StefansAI/LCD-DisplayController/docs/assets/images/photo2.png

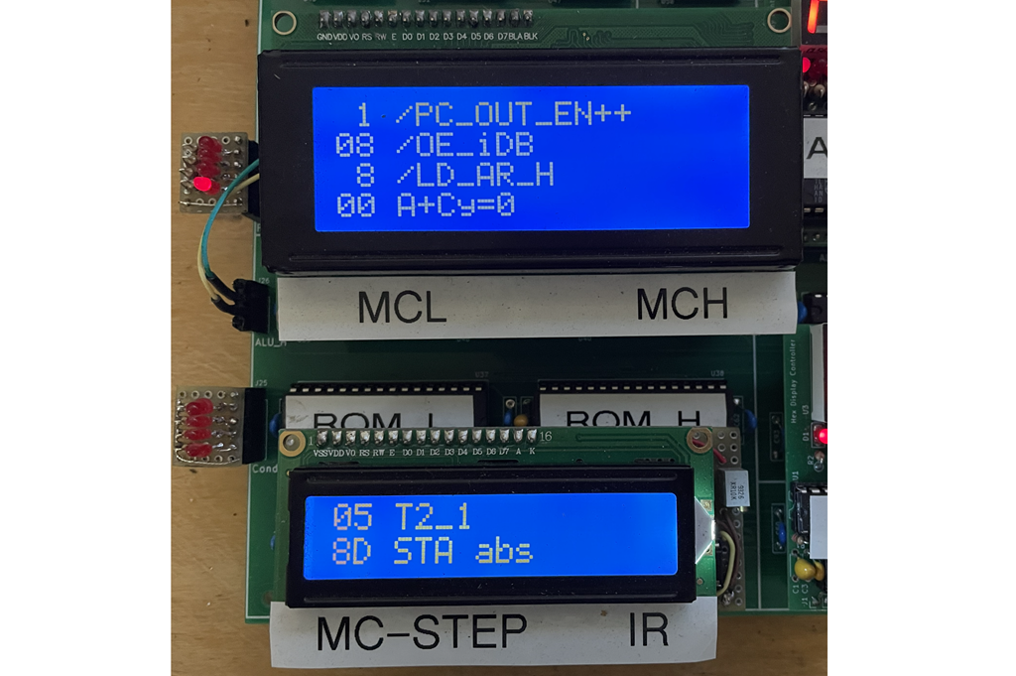
docs/assets/images/photo2.png
